derekdotdev/cat-tracker/Documentation/Schematics/JunoTracker5000FritzingSketch-EthernetShield-SoundSensor_bb.jpg

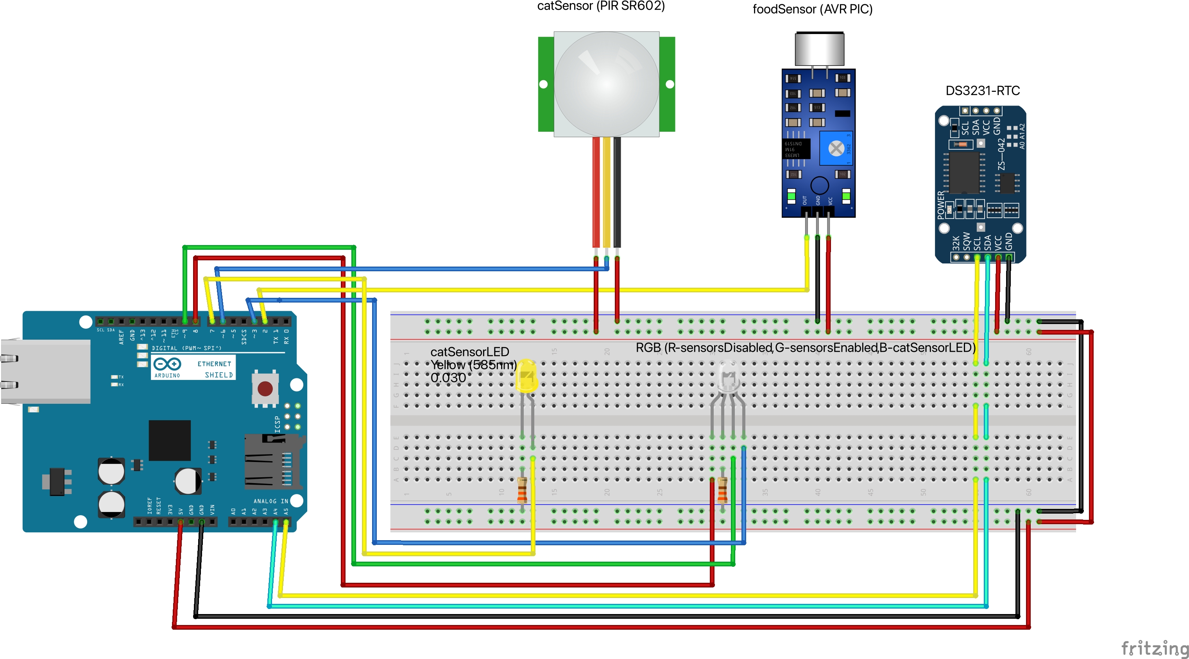
Documentation/Schematics/JunoTracker5000FritzingSketch-EthernetShield-SoundSensor_bb.jpg
